Ferivas/RELOJ_GPS/SCH/TarjetaPS2serial/PS2teclado_PCB.pdf

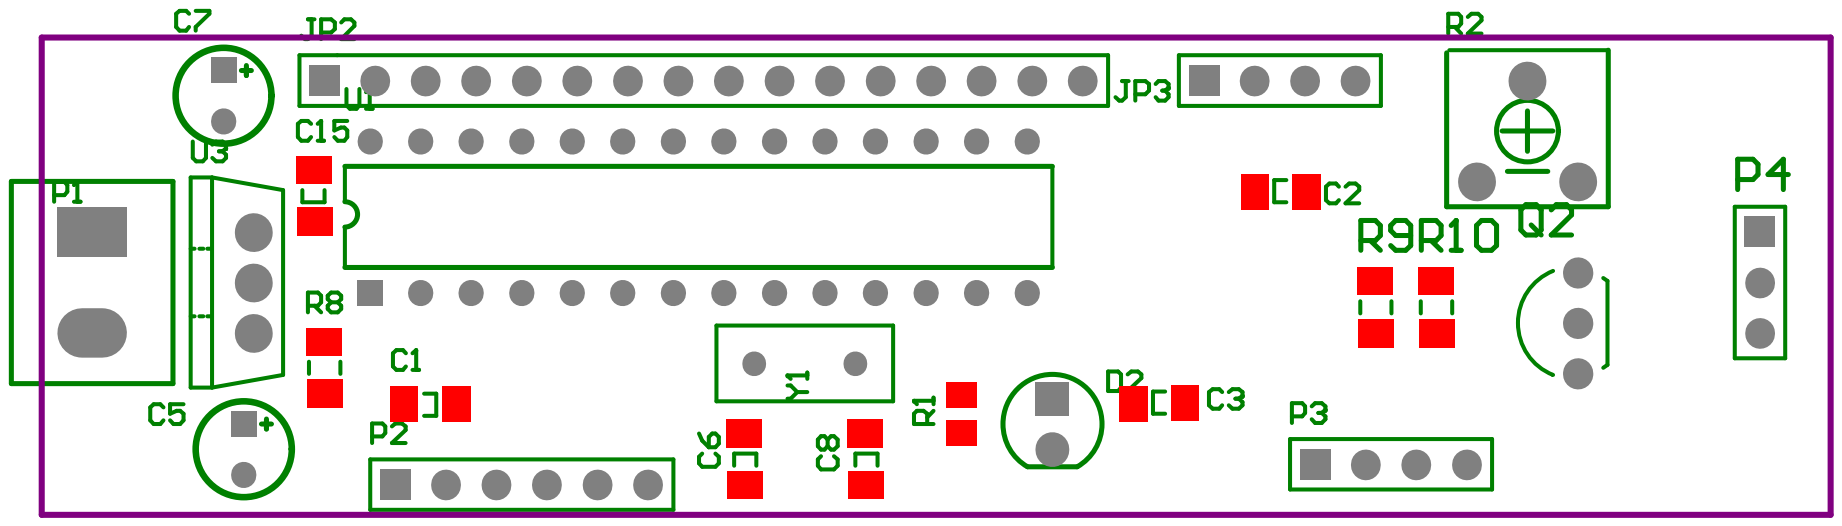
[picture p21: page 1]

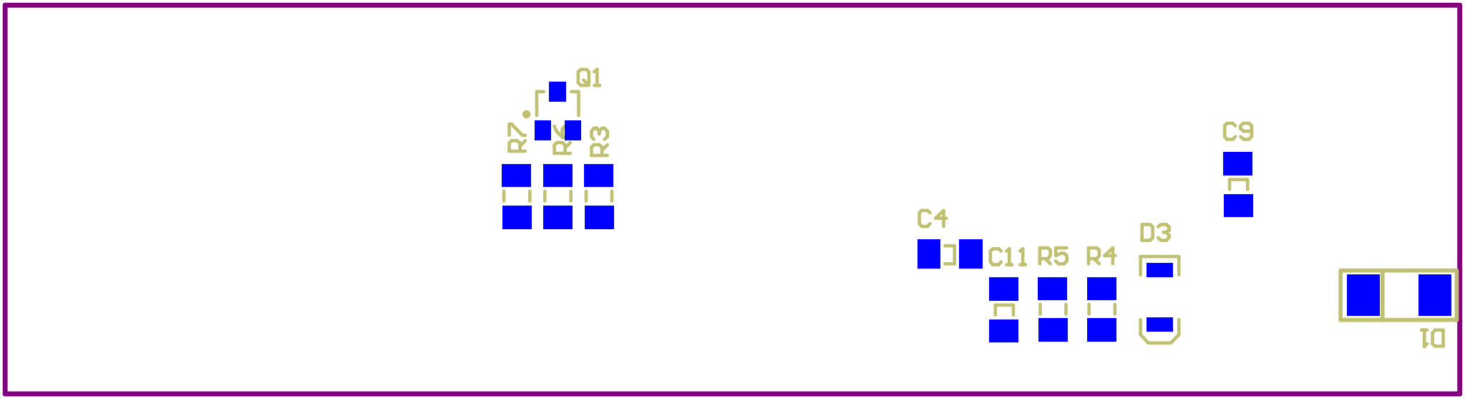
[picture p22: figure]
