Ferivas/RELOJ_GPS/SCH/TarjetaPS2serial/PS2teclado_SCH.pdf

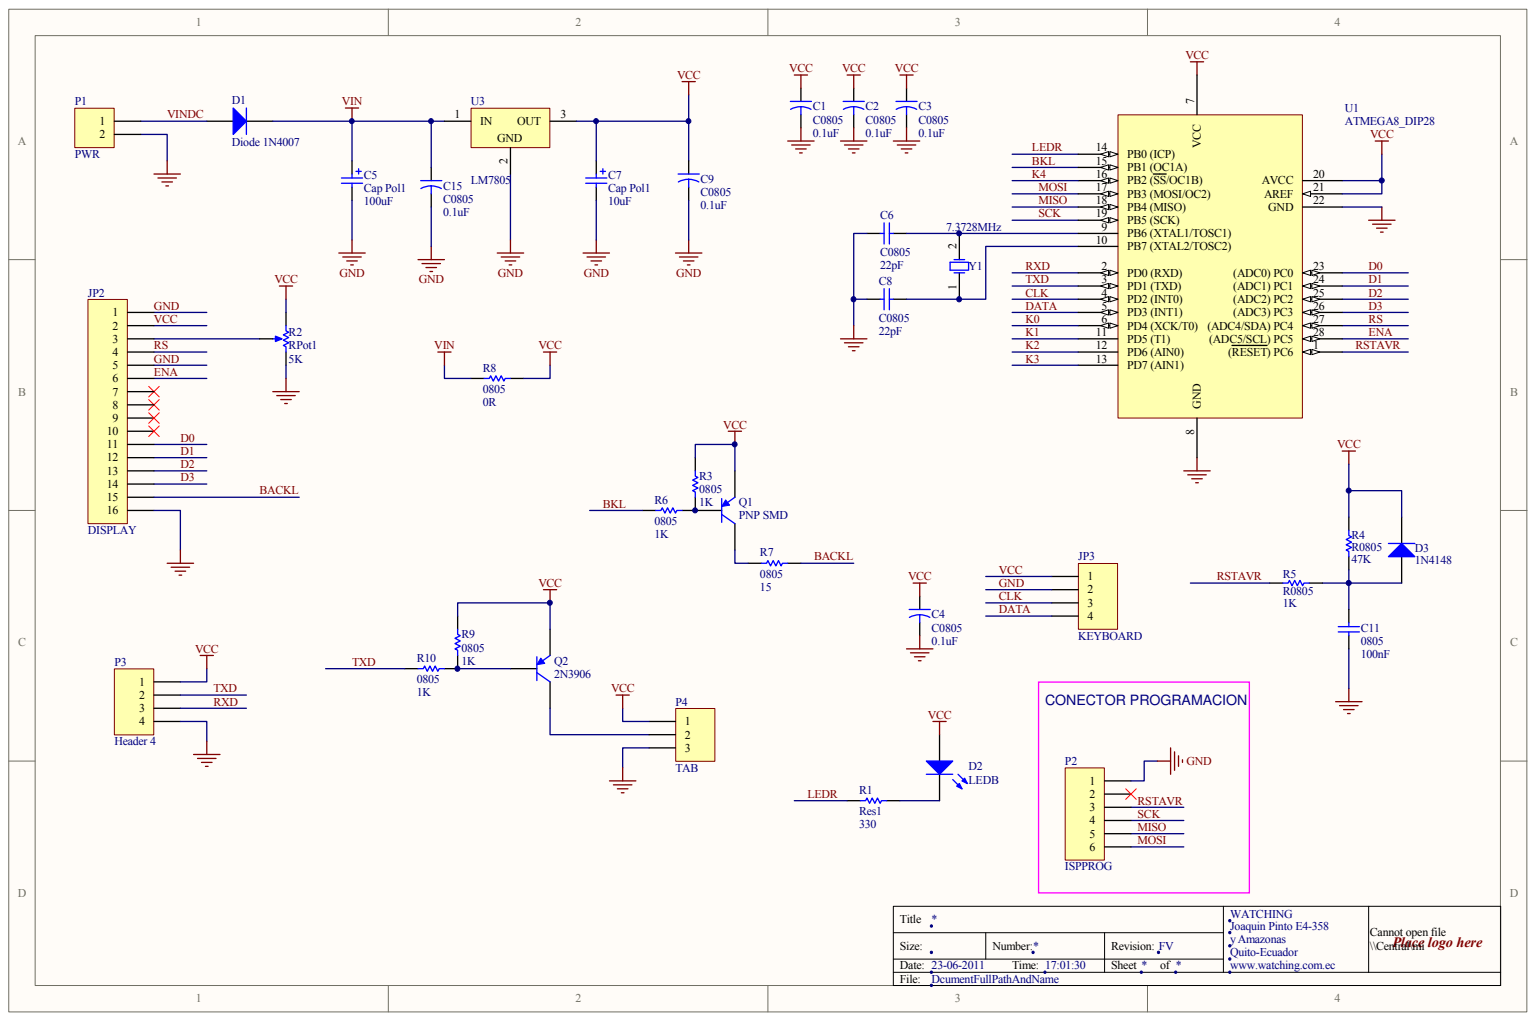
[picture p23: page 1]
