Ferivas/RELOJ_GPS/SCH/JLCPCB/PCB_PCB_DRV_A6282_2021-11-23.pcbdoc_2022-02-17.pdf

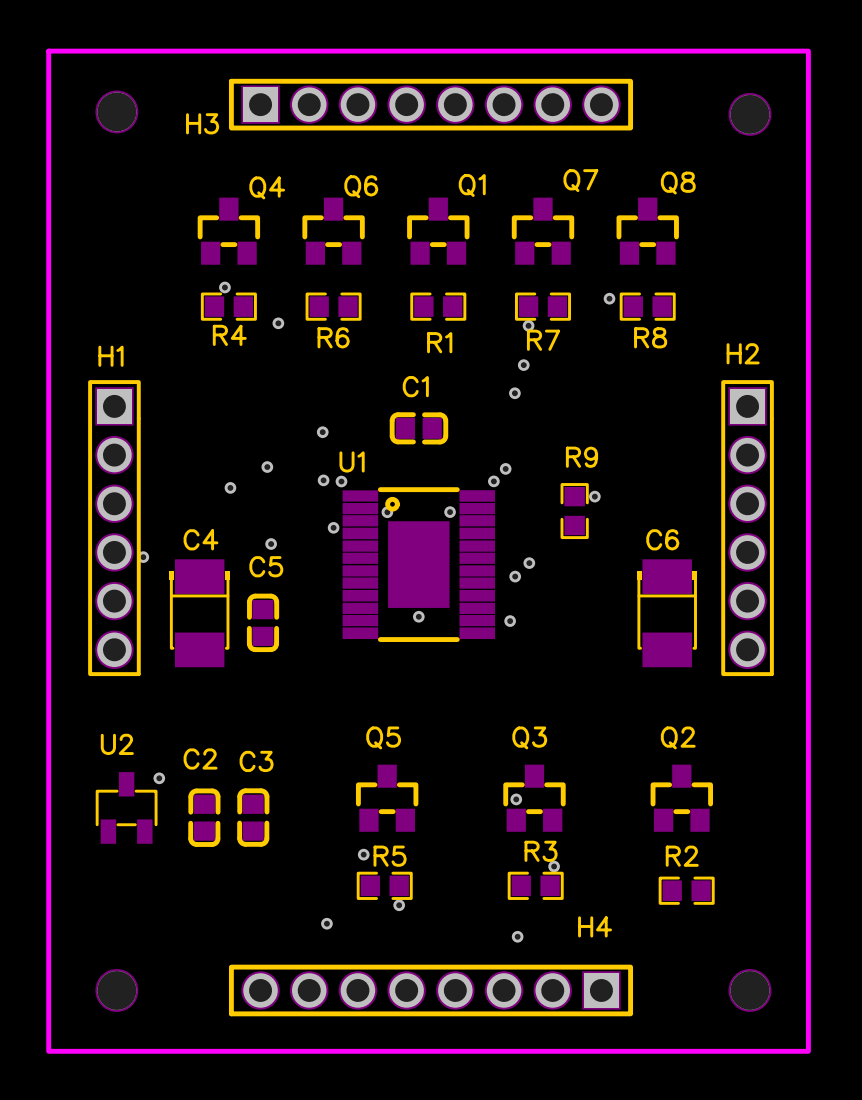
[picture p24: page 1]
